K0-p/Garfield-Wheel/sw/img/drunk_driving.jpg

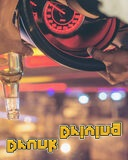
sw/img/drunk_driving.jpg
