K0-p/Garfield-Wheel/sw/img/launch.png

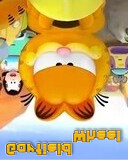
sw/img/launch.png
