K0-p/Garfield-Wheel/sw/src/menu.c

///**
// * Interfaces the ST735
// *
// * 	No cheeseburger relevant

#include "menu.h"
#include "../img/pipe.h"
#include "switches.h"

#define GARF_TEXT 0x041f

uint32_t menu_state;
uint32_t headspot;
uint32_t subspot;
uint32_t genable;
uint32_t gstate;

uint32_t gyro_state;
uint32_t ged;
int gedspot;

//initial display screen upon device launch
void displayinit(void){
	ged = 0;
	gedspot = 0;
	ST7735_InitR(INITR_REDTAB);
	//ST7735_FillScreen(ST7735_BLACK);
  ST7735_SetCursor(0, 0);
	Unified_Port_Init();
	int x = 0;
	genable = 1;
  int y = 159;	//height-1
	//inputs: x,y,file,width,heigth
	ST7735_DrawBitmap(x, y, launch, 128, 160);
	menu_state = 0;
	headspot = 0;
	gstate = 1;
	subspot = 0;
	//printf("%d\n",gyro_state);
	return;
}

void drawhead(uint32_t spot){
	ST7735_FillRect(0,43,HEAD__WIDTH,155,0x0000);
	if(spot == 0) ST7735_DrawBitmap(0, 75, head, HEAD__WIDTH, HEAD__HEIGHT);
	if(spot == 1) ST7735_DrawBitmap(0, 115, head, HEAD__WIDTH, HEAD__HEIGHT);
	if(spot == 2) ST7735_DrawBitmap(0, 155, head, HEAD__WIDTH, HEAD__HEIGHT);
	return;
}

//menu handler
void menu(void){
	ST7735_FillScreen(0x0000);
	ST7735_DrawBitmap(0, MENU_HEIGHT-5, menu_text, 128, MENU_HEIGHT);
	//headspot = 0;
	//drawhead();
	ST7735_DrawString(6,6,"CONFIGURATION", GARF_TEXT);
	ST7735_DrawString(6,10,"INFORMATION", GARF_TEXT);
	ST7735_DrawString(6,14,"CREDITS", GARF_TEXT);
	return;
}

//config handler
void submenu(void){
	ST7735_FillScreen(0x0000);
	if(genable) ST7735_DrawString(6,2,"GYRO ENABLE", ST7735_GREEN);
	else ST7735_DrawString(6,2,"GYRO ENABLE", ST7735_RED);
	ST7735_DrawString(6,6,"GARFIELD KART", GARF_TEXT);
	ST7735_DrawString(6,10,"DRUNK DRIVING", GARF_TEXT);
	ST7735_DrawString(6,14,"STANDARD", GARF_TEXT);
	return;
}

//gstate(4 bits of data):
//	xxxx
// [gyro enabled]	[garf kart] [drunk mode] [standard]
char std[] = {'S','T','A','N','D','A','R','D'};
void ingame(void){
	ST7735_FillScreen(0x0000);
	gyro_state = gstate;
	gedspot = -31;
	ged = 0;
	ST7735_DrawString(3,4,"ENTERING", GARF_TEXT);
		while(gedspot !=129){
			ged++;
			if(ged == 3){
				ged = 0;
				gedspot++;
					if(gedspot == 20){
						ST7735_DrawChar(70, 35, '.', GARF_TEXT, 0, 2);
					}
					if(gedspot == 45){
						ST7735_DrawChar(77, 35, '.', GARF_TEXT, 0, 2);
					}
					if(gedspot == 70){
						ST7735_DrawChar(84, 35, '.', GARF_TEXT, 0, 2);
					}
					if(gedspot == 95){
						ST7735_DrawChar(91, 35, '.', GARF_TEXT, 0, 2);
					}
			}
		ST7735_DrawBitmap(gedspot, 137, head, HEAD__WIDTH, HEAD__HEIGHT);
	}
	
	if(((gstate&0x2)>>1) == 1){
		//ST7735_FillScreen(0x0000);
		//printf("drunk mode \n");
		ST7735_DrawBitmap(0, 159, drunk_driving, 128, 160);
	}
	if(((gstate&0x4)>>2) == 1){
		//printf("garf mode \n");
		ST7735_DrawBitmap(0, 159, launch, 128, 160);
	}
	if((gstate&0x1) == 1){
		ST7735_DrawBitmap(0, 159, launch, 128, 160);
		ST7735_SetCursor(0, 0);
		//ST7735_DrawChar(int16_t x, int16_t y, char c, int16_t textColor, int16_t bgColor, uint8_t size)
		//size      number of pixels per character pixel (e.g. size==2 prints each pixel of font as 2x2 square)
		for(uint32_t i = 0; i<8; i++) ST7735_DrawChar(5+12*i, 1, std[i], 0x1d9d, 0xfdb2, 2);
	}
	return;
}

void config(void){
	submenu();
	return;
}

void headbounce(void){
	if((menu_state == 3) || (menu_state == 4)){
		ged++;
		if(ged == 5){
			ged = 0;
			gedspot++;
			if(gedspot == 129){
				gedspot = -31;
				//while(1){}
			}
		}
		ST7735_DrawBitmap(gedspot, 137, head, HEAD__WIDTH, HEAD__HEIGHT);
	}
	return;
}

void info(void){
	ST7735_FillScreen(0x0000);
	ST7735_DrawString(5,2,"INFORMATION", GARF_TEXT);
	ST7735_DrawString(1,4,"This system is an", 0x1d9d);
	ST7735_DrawString(1,5,"HID-compliant game", 0x1d9d);
	ST7735_DrawString(1,6,"controller. There", 0x1d9d);
	ST7735_DrawString(1,7,"are 3 modes that can", 0x1d9d);
	ST7735_DrawString(1,8,"be configured in the", 0x1d9d);
	ST7735_DrawString(1,9,"config submenu.   :)", 0x1d9d);
	gedspot = 0;
	ST7735_DrawString(1,15,"funny cat go vroom", 0x1d9d);
	return;
}

void credits(void){
	ST7735_FillScreen(0x0000);
	ST7735_DrawString(7,2,"CREDITS", GARF_TEXT);
	ST7735_DrawString(1,4,"Garfield Wheel is", 0x1d9d);
	ST7735_DrawString(1,5,"the brainchild of", 0x1d9d);
	ST7735_DrawString(1,6,"Gabriel Moore and", 0x1d9d);
	ST7735_DrawString(1,7,"Calvin Heischman in", 0x1d9d);
	ST7735_DrawString(1,8,"ECE 445L (year 2024)", 0x1d9d);
	gedspot = 0;
	ST7735_DrawString(1,15,"--and Garfield (duh)", 0x1d9d);
	return;
}

// *	Buttons: [start,up,right,down,left]
void menuhandler(uint32_t butt){
	//invert so 1 = press
	butt = (~butt)&0x1F;
	uint32_t next_state = press_task(menu_state,butt);
	//display init
	if(next_state == 0){
		if(menu_state != 0) ST7735_DrawBitmap(0, 159, launch, 128, 160);
		menu_state = 0;
		return;
	}
	//menu
	if(next_state == 1){
		if(menu_state != 1) menu();
		else{
			//up
			if(butt == 0x8){
				if(headspot == 0) headspot = 2;
				else headspot--;
			}
			//down
			if(butt == 0x2){
				if(headspot == 2) headspot = 0;
				else headspot++;
			}
		}
		drawhead(headspot);
		menu_state = 1;
		return;
	}
	//choose submenu
	if(next_state == 69){
		//launch config menu
		if(headspot == 0){
			ST7735_FillScreen(0x0000);
			if(menu_state != 2) config();
			menu_state = 2;
			drawhead(subspot);
		}
		//launch info menu
		if(headspot == 1){
			menu_state = 3;
			info();
		}
		//launch credits menu
		if(headspot == 2){
			menu_state = 4;
			credits();
		}
		//printf("%d\n",headspot);
		return;
	}
	//config
	if(next_state == 2){
		//right
		if(butt == 0x4){
			genable ^= 1;
		}
		//update enable color
		if(genable) ST7735_DrawString(6,2,"GYRO ENABLE", ST7735_GREEN);
		else ST7735_DrawString(6,2,"GYRO ENABLE", ST7735_RED);
		//up
		if(butt == 0x8){
			if(subspot == 0) subspot = 2;
			else subspot--;
		}
		//down
		if(butt == 0x2){
			if(subspot == 2) subspot = 0;
			else subspot++;
		}
		drawhead(subspot);
		return;
	}
	//info	-- should never get here (not interactive)
	if(next_state == 3){
		return;
	}
	//credits	-- should never get here (not interactive)
	if(next_state == 4){
		return;
	}
	//in game
	//else return;
	else{
		if(subspot == 0) gstate = 4;
		if(subspot == 1) gstate = 2;
		if(subspot == 2) gstate = 1;
		gstate = (genable<<3) + gstate;
		if(menu_state != 5) ingame();
		menu_state = 5;
		//printf("ENTERD\n");
		return;
	}
}
