K0-p/Garfield-Wheel/sw/inc/SysTick.c

// SysTick.c
// Runs on LM4F120/TM4C123
// Provide functions that initialize the SysTick module, wait at least a
// designated number of clock cycles, and wait approximately a multiple
// of 10 milliseconds using busy wait.  After a power-on-reset, the
// LM4F120 gets its clock from the 16 MHz precision internal oscillator,
// which can vary by +/- 1% at room temperature and +/- 3% across all
// temperature ranges.  
// Daniel Valvano
// Jan 2, 2020

/* This example accompanies the books
   "Embedded Systems: Introduction to ARM Cortex M Microcontrollers",
   ISBN: 978-1469998749, Jonathan Valvano, copyright (c) 2020
   Volume 1, Program 4.7
   
   "Embedded Systems: Real Time Interfacing to ARM Cortex M Microcontrollers",
   ISBN: 978-1463590154, Jonathan Valvano, copyright (c) 2020
   Program 2.11, Section 2.6

 Copyright 2020 by Jonathan W. Valvano, valvano@mail.utexas.edu
    You may use, edit, run or distribute this file
    as long as the above copyright notice remains
 THIS SOFTWARE IS PROVIDED "AS IS".  NO WARRANTIES, WHETHER EXPRESS, IMPLIED
 OR STATUTORY, INCLUDING, BUT NOT LIMITED TO, IMPLIED WARRANTIES OF
 MERCHANTABILITY AND FITNESS FOR A PARTICULAR PURPOSE APPLY TO THIS SOFTWARE.
 VALVANO SHALL NOT, IN ANY CIRCUMSTANCES, BE LIABLE FOR SPECIAL, INCIDENTAL,
 OR CONSEQUENTIAL DAMAGES, FOR ANY REASON WHATSOEVER.
 For more information about my classes, my research, and my books, see
 http://users.ece.utexas.edu/~valvano/
 */

#include <stdint.h>
#include "../inc/tm4c123gh6pm.h"
#define NVIC_ST_CTRL_COUNT      0x00010000  // Count flag
#define NVIC_ST_CTRL_CLK_SRC    0x00000004  // Clock Source
#define NVIC_ST_CTRL_INTEN      0x00000002  // Interrupt enable
#define NVIC_ST_CTRL_ENABLE     0x00000001  // Counter mode
#define NVIC_ST_RELOAD_M        0x00FFFFFF  // Counter load value

// Initialize SysTick with busy wait running at bus clock.
void SysTick_Init(void){
  NVIC_ST_CTRL_R = 0;                   // disable SysTick during setup
  NVIC_ST_RELOAD_R = NVIC_ST_RELOAD_M;  // maximum reload value
  NVIC_ST_CURRENT_R = 0;                // any write to current clears it
	NVIC_ST_CTRL_R = 0x00000005;
                                        // enable SysTick with core clock
  //NVIC_ST_CTRL_R = NVIC_ST_CTRL_ENABLE+NVIC_ST_CTRL_CLK_SRC;
}

// Time delay using busy wait.
// The delay parameter is in units of the core clock. (units of 20 nsec for 50 MHz clock)
//void SysTick_Wait(uint32_t delay){
//  volatile uint32_t elapsedTime;
//  uint32_t startTime = NVIC_ST_CURRENT_R;
//  do{
//    elapsedTime = (startTime-NVIC_ST_CURRENT_R)&0x00FFFFFF;
//  }
//  while(elapsedTime <= delay);
//}
// The delay parameter is in units of the 80 MHz core clock. (12.5 ns)
void SysTick_Wait(uint32_t delay){
  NVIC_ST_RELOAD_R = delay-1;  // number of counts to wait
  NVIC_ST_CURRENT_R = 0;       // any value written to CURRENT clears
  while((NVIC_ST_CTRL_R&0x00010000)==0){ // wait for count flag
  }
}

// Time delay using busy wait.
// This assumes 16 MHz system clock.
void SysTick_Wait10ms(uint32_t delay){
  uint32_t i;
  for(i=0; i<delay; i++){
    SysTick_Wait(160000);  // wait 10ms (assumes 16 MHz clock)
  }
}
// Time delay using busy wait.
// This assumes 50 MHz system clock.
void SysTick50_Wait10ms(uint32_t delay){
  uint32_t i;
  for(i=0; i<delay; i++){
    SysTick_Wait(500000);  // wait 10ms (assumes 50 MHz clock)
  }
}
// Time delay using busy wait.
// This assumes 80 MHz system clock.
void SysTick80_Wait10ms(uint32_t delay){
  uint32_t i;
  for(i=0; i<delay; i++){
    SysTick_Wait(80);  // wait 1 microsecond
  }
}

uint32_t Time;
// start the stopwatch
void SysTick_Start(void){
  Time = NVIC_ST_CURRENT_R;
}
// end the stopwatch, and return elased time in bus cycles
uint32_t SysTick_Stop(void){
  return (Time-NVIC_ST_CURRENT_R)&0x00FFFFFF;
}
