K0-p/Garfield-Wheel/sw/inc/Timer0A.c

// Timer0A.c
// Runs on LM4F120/TM4C123
// Use Timer0A in periodic mode to request interrupts at a particular
// period.
// Daniel Valvano
// Jan 4, 2020

/* This example accompanies the book
   "Embedded Systems: Introduction to ARM Cortex M Microcontrollers"
   ISBN: 978-1469998749, Jonathan Valvano, copyright (c) 2020
   Volume 1, Program 9.8

  "Embedded Systems: Real Time Interfacing to ARM Cortex M Microcontrollers",
   ISBN: 978-1463590154, Jonathan Valvano, copyright (c) 2020
   Volume 2, Program 7.5, example 7.6

 Copyright 2020 by Jonathan W. Valvano, valvano@mail.utexas.edu
    You may use, edit, run or distribute this file
    as long as the above copyright notice remains
 THIS SOFTWARE IS PROVIDED "AS IS".  NO WARRANTIES, WHETHER EXPRESS, IMPLIED
 OR STATUTORY, INCLUDING, BUT NOT LIMITED TO, IMPLIED WARRANTIES OF
 MERCHANTABILITY AND FITNESS FOR A PARTICULAR PURPOSE APPLY TO THIS SOFTWARE.
 VALVANO SHALL NOT, IN ANY CIRCUMSTANCES, BE LIABLE FOR SPECIAL, INCIDENTAL,
 OR CONSEQUENTIAL DAMAGES, FOR ANY REASON WHATSOEVER.
 For more information about my classes, my research, and my books, see
 http://users.ece.utexas.edu/~valvano/
 */
#include <stdint.h>
#include "../inc/tm4c123gh6pm.h"
#include "../inc/CortexM.h"
#include "../inc/Timer0A.h"

#define NVIC_EN0_INT19          0x00080000  // Interrupt 19 enable
#define TIMER_CFG_16_BIT        0x00000004  // 16-bit timer configuration,
                                            // function is controlled by bits
                                            // 1:0 of GPTMTAMR and GPTMTBMR
#define TIMER_TAMR_TACDIR       0x00000010  // GPTM Timer A Count Direction
#define TIMER_TAMR_TAMR_PERIOD  0x00000002  // Periodic Timer mode
#define TIMER_CTL_TAEN          0x00000001  // GPTM TimerA Enable
#define TIMER_IMR_TATOIM        0x00000001  // GPTM TimerA Time-Out Interrupt
                                            // Mask
#define TIMER_ICR_TATOCINT      0x00000001  // GPTM TimerA Time-Out Raw
                                            // Interrupt
#define TIMER_TAILR_TAILRL_M    0x0000FFFF  // GPTM TimerA Interval Load
                                            // Register Low
																						
#define PF3   (*((volatile uint32_t *)0x40025020)) // GREEN LED


static void (*PeriodicTask0)(void);   // user function
uint32_t chiefidx;
uint32_t peener;
uint32_t testiclehernia;

uint32_t cc2;
uint32_t cc4;

uint32_t envelope;

// ***************** Timer0A_Init ****************
// Activate Timer0A interrupts to run user task periodically
// Inputs:  task is a pointer to a user function
//          period in 12.5ns units
//          priority 0 (highest) to 7 (lowest)
// Outputs: none
void Timer0A_Init(void(*task)(void), uint32_t period, uint32_t priority){
  SYSCTL_RCGCTIMER_R |= 0x01;      // 0) activate timer0
  PeriodicTask0 = task;            // user function (this line also allows time to finish activating)
  TIMER0_CTL_R &= ~0x00000001;     // 1) disable timer0A during setup
  TIMER0_CFG_R = 0x00000000;       // 2) configure for 32-bit timer mode
  TIMER0_TAMR_R = 0x00000002;      // 3) configure for periodic mode, default down-count settings
  TIMER0_TAILR_R = period-1;       // 4) reload value
  TIMER0_TAPR_R = 0;               // 5) 12.5ns timer0A
  TIMER0_ICR_R = 0x00000001;       // 6) clear timer0A timeout flag
  TIMER0_IMR_R |= 0x00000001;      // 7) arm timeout interrupt
  NVIC_PRI4_R = (NVIC_PRI4_R&0x00FFFFFF)|(priority<<29); 
  NVIC_EN0_R = NVIC_EN0_INT19;     // 9) enable interrupt 19 in NVIC
  TIMER0_CTL_R |= 0x00000001;      // 10) enable timer0A
	chiefidx = 0;
	testiclehernia = 2;
	cc2 = 2;
	cc4 = 4;
	envelope = 0;
}

void Timer0A_Handler(void){
  TIMER0_ICR_R = TIMER_ICR_TATOCINT;// acknowledge timer0A timeout
  (*PeriodicTask0)();                // execute user task
}
void Timer0A_Stop(void){
  NVIC_EN0_R = 1<<19;            // 9) disable interrupt 19 in NVIC
  TIMER0_CTL_R = 0x00000000;     // 10) disable timer0A
}

void fart(void){
	if(testiclehernia == 2){
		cc2 --;
		if(cc2 == 0){
			cc2 = 2;
		}
		else return;
	}
	if(testiclehernia == 4){
		cc4 --;
		if(cc4 == 0){
			cc4 = 4;
		}
		else return;
	}
	if(peener){
		//envelope = 0;
		PF3 ^= 0x08;
		chiefidx ++;
		if(chiefidx > 28) chiefidx = 0;
		uint32_t volatile time;
		uint32_t n = 25;
    while (n){
        time = 727240 * 2 / 91;  // 10msec
        while (time){
            --time;
        }
        --n;
    }
	}
	return;
}
