K0-p/Garfield-Wheel/sw/inc/Timer1A.c

// Timer1A.c
// Runs on LM4F120/TM4C123
// Use TIMER1 in 32-bit periodic mode to request interrupts at a periodic rate
// Daniel Valvano
// Jan 1, 2020

/* This example accompanies the book
   "Embedded Systems: Real Time Interfacing to Arm Cortex M Microcontrollers",
   ISBN: 978-1463590154, Jonathan Valvano, copyright (c) 2020
  Program 7.5, example 7.6

 Copyright 2020 by Jonathan W. Valvano, valvano@mail.utexas.edu
    You may use, edit, run or distribute this file
    as long as the above copyright notice remains
 THIS SOFTWARE IS PROVIDED "AS IS".  NO WARRANTIES, WHETHER EXPRESS, IMPLIED
 OR STATUTORY, INCLUDING, BUT NOT LIMITED TO, IMPLIED WARRANTIES OF
 MERCHANTABILITY AND FITNESS FOR A PARTICULAR PURPOSE APPLY TO THIS SOFTWARE.
 VALVANO SHALL NOT, IN ANY CIRCUMSTANCES, BE LIABLE FOR SPECIAL, INCIDENTAL,
 OR CONSEQUENTIAL DAMAGES, FOR ANY REASON WHATSOEVER.
 For more information about my classes, my research, and my books, see
 http://users.ece.utexas.edu/~valvano/
 */
#include <stdint.h>
#include "../inc/tm4c123gh6pm.h"
#include "../inc/DAC.h"

#define PF2   (*((volatile uint32_t *)0x40025010)) // BLUE LED


const uint16_t Wave[64] = {2048,2249,2447,2642,2831,3013,3185,3347,3495,3630,3750,3853,3939,4007,4056,4085,4095,4085,4056,4007,3939,3853,3750,3630,3495,3347,3185,3013,2831,2642,2447,2249,2048,1847,1649,1454,1265,1083,911,749,601,466,346,243,157,89,40,11,1,11,40,89,157,243,346,466,601,749,911,1083,1265,1454,1649,1847};

void (*PeriodicTask1)(void);   // user function
uint32_t i = 0;

// ***************** TIMER1A_Init ****************
// Activate TIMER1A interrupts to run user task periodically
// Inputs:  task is a pointer to a user function
//          period in units (1/clockfreq)
//          priority 0 (highest) to 7 (lowest)
// Outputs: none
/*void Timer1A_Init(uint32_t period, uint32_t priority){
  SYSCTL_RCGCTIMER_R |= 0x02;   // 0) activate TIMER1
  //PeriodicTask1 = task;         // user function
	TIMER1_CTL_R &= ~0x00000001; // disable timer1A during setup
  TIMER1_CFG_R = 0x00000000;    // 2) configure for 32-bit mode
  TIMER1_TAMR_R = 0x00000002;   // 3) configure for periodic mode, default down-count settings
  TIMER1_TAILR_R = 0xFFFFF;    // 4) reload value
  TIMER1_TAPR_R = 0;            // 5) bus clock resolution
  TIMER1_ICR_R = 0x00000001;    // 6) clear TIMER1A timeout flag
  TIMER1_IMR_R = 0x00000001;    // 7) arm timeout interrupt
  NVIC_PRI5_R = (NVIC_PRI5_R&0xFFFF00FF)|(priority<<13); // priority 
// interrupts enabled in the main program after all devices initialized
// vector number 37, interrupt number 21
  NVIC_EN0_R = 1<<21;           // 9) enable IRQ 21 in NVIC
	TIMER1_CTL_R |= 0x00000001; // enable timer1A
}*/

void Timer1A_Init(uint32_t period, uint32_t priority){
  SYSCTL_RCGCTIMER_R |= 0x02;   // 0) activate TIMER1
  //PeriodicTask1 = task;         // user function
  TIMER1_CTL_R = 0x00000000;    // 1) disable TIMER1A during setup
  TIMER1_CFG_R = 0x00000000;    // 2) configure for 32-bit mode
  TIMER1_TAMR_R = 0x00000002;   // 3) configure for periodic mode, default down-count settings
  TIMER1_TAILR_R = 60000;    // 4) reload value
  TIMER1_TAPR_R = 0;            // 5) bus clock resolution
  TIMER1_ICR_R = 0x00000001;    // 6) clear TIMER1A timeout flag
  TIMER1_IMR_R = 0x00000001;    // 7) arm timeout interrupt
  NVIC_PRI5_R = (NVIC_PRI5_R&0xFFFF00FF)|(priority<<13); // priority 
// interrupts enabled in the main program after all devices initialized
// vector number 37, interrupt number 21
  NVIC_EN0_R = 1<<21;           // 9) enable IRQ 21 in NVIC
  TIMER1_CTL_R = 0x00000001;    // 10) enable TIMER1A
}

void Timer1A_Handler(void){
		TIMER1_ICR_R = TIMER_ICR_TATOCINT;
	//fix when made global
	/*uint32_t volatile time;
	uint32_t n = 10;
    while (n){
        time = 727240 * 2 / 91;  // 10msec
        while (time){
            --time;
        }
        --n;
    }*/
	PF2 ^= 0x04;
  //TIMER0_ICR_R = TIMER_ICR_TATOCINT; // acknowledge
  i = (i+1)&0x3F; // 0 to 63
  dac_output(Wave[i]);
}


void Timer1A_Stop(void){
  NVIC_DIS0_R = 1<<21;        // 9) disable IRQ 21 in NVIC
  TIMER1_CTL_R = 0x00000000;  // 10) disable timer1A
}

void Timer1A_Start(void){
	NVIC_EN0_R = 1<<21;           // 9) enable IRQ 21 in NVIC
  TIMER1_CTL_R = 0x00000001;    // 10) enable TIMER1A
}

void Timer1A_ChangePeriod(uint32_t newPeriod){
	TIMER1_TAILR_R = newPeriod - 1;
}
